Atharv-Shukla-987/DEVBOARD/img/Footprint1.png

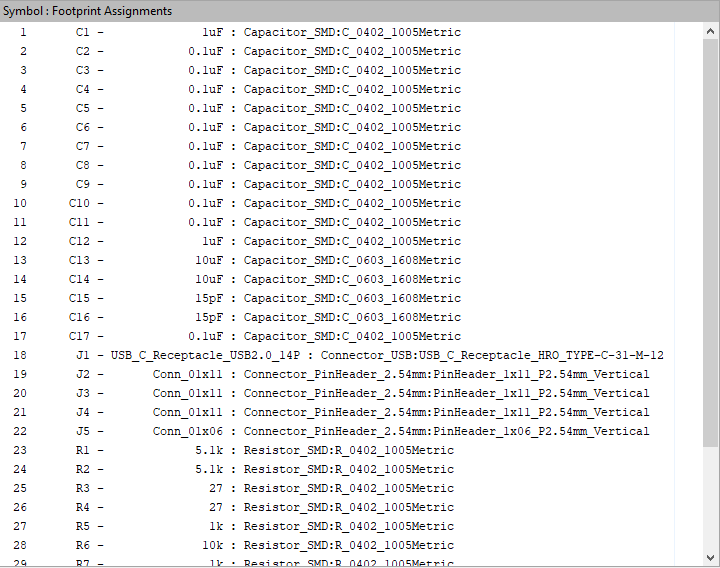
img/Footprint1.png
