Atharv-Shukla-987/DEVBOARD/img/Pcb editor.png

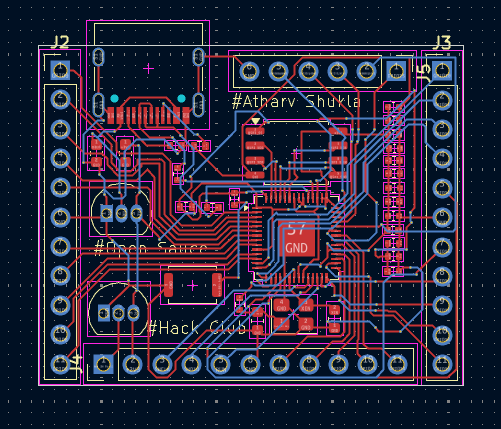
img/Pcb editor.png
