Atharv-Shukla-987/DEVBOARD/img/Pcb_3d_back.png

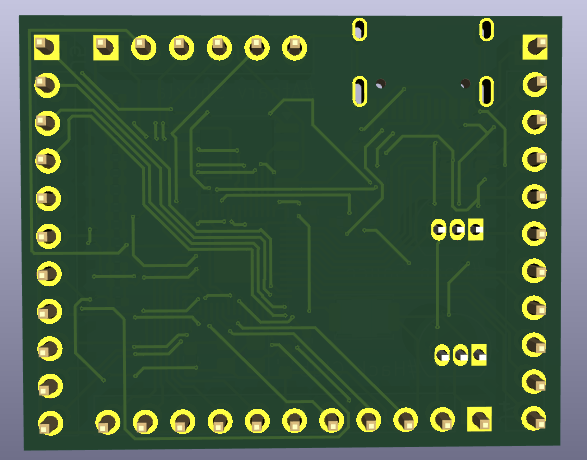
img/Pcb_3d_back.png
