Atharv-Shukla-987/DEVBOARD/img/Schematics/Flash Strorage.png

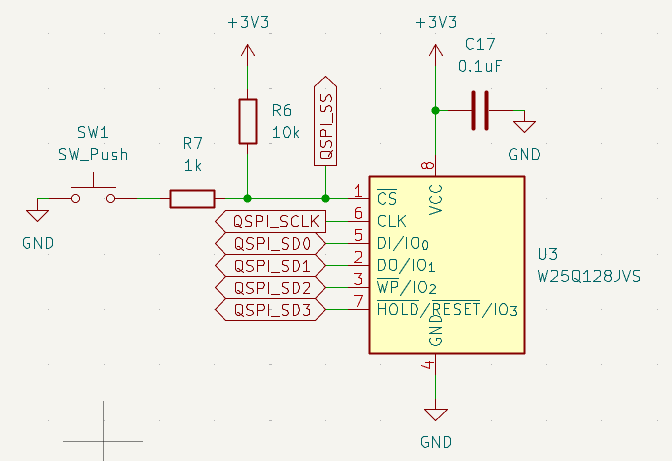
img/Schematics/Flash Strorage.png
